eez-open/CF-DIC/EEZ CF-DIC r5B7 Sheet1of3.png

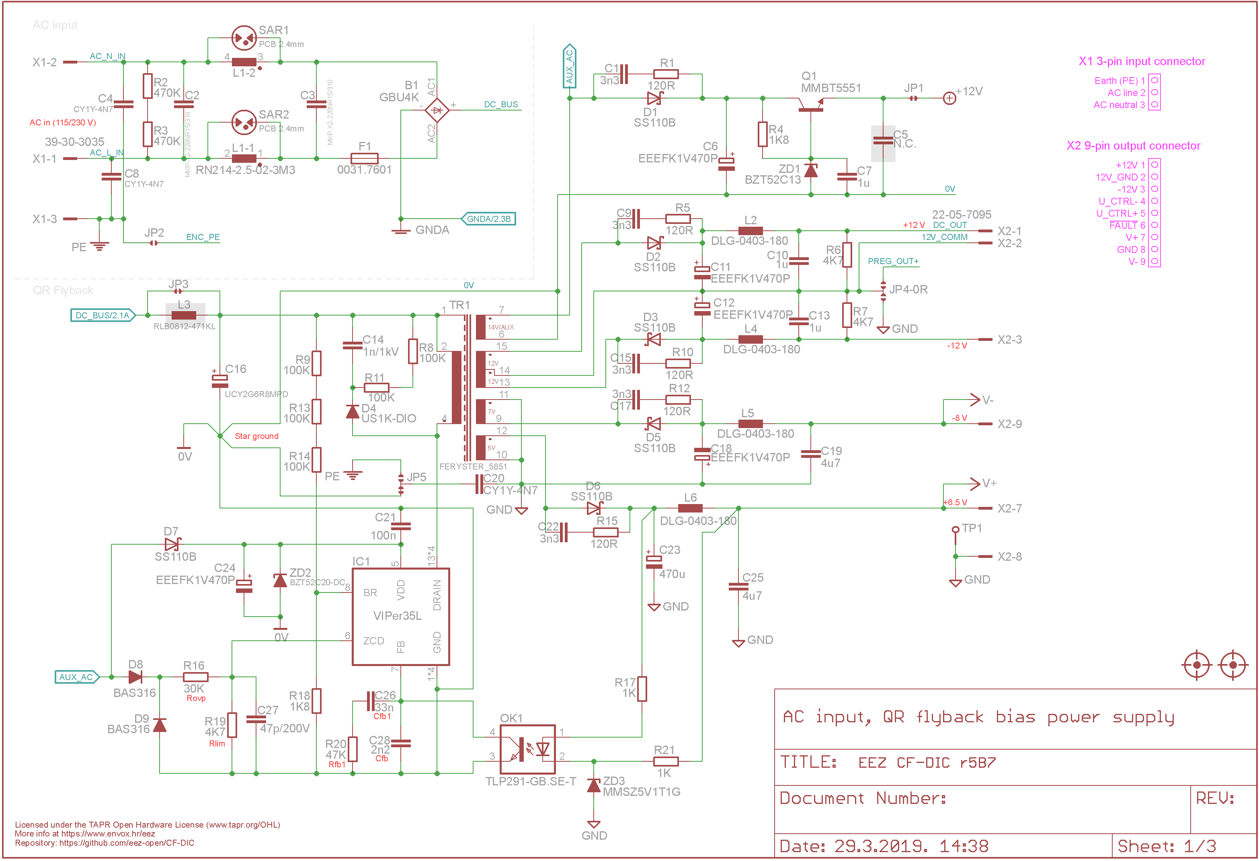
EEZ CF-DIC r5B7 Sheet1of3.png
