eez-open/CF-DIC/EEZ CF-DIC r5B7 Sheet2of3.png

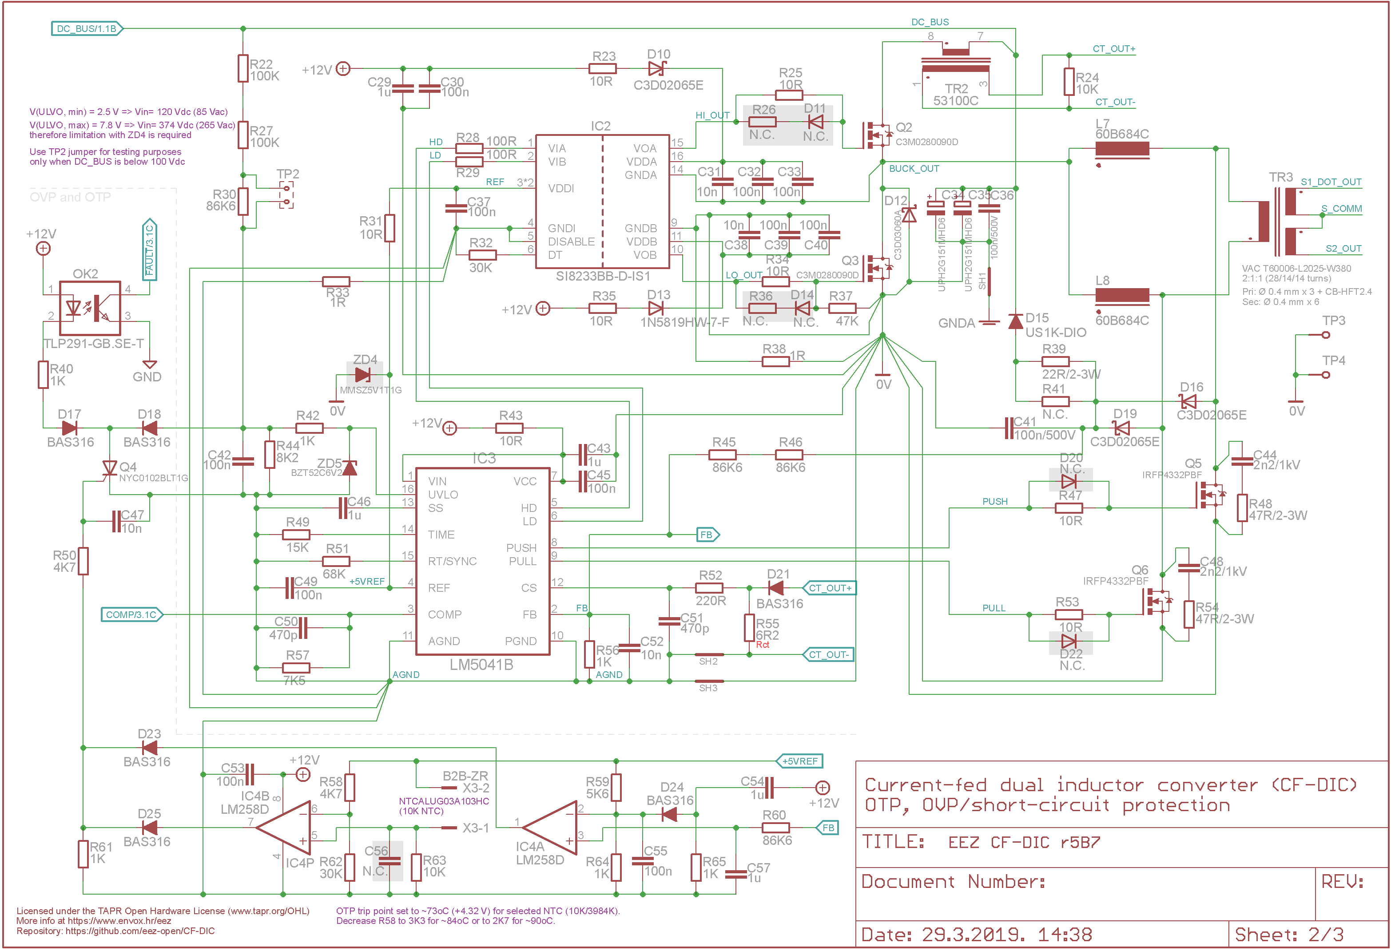
EEZ CF-DIC r5B7 Sheet2of3.png
