eez-open/CF-DIC/Images/CF-DIC_PCB_parts_bottom.png

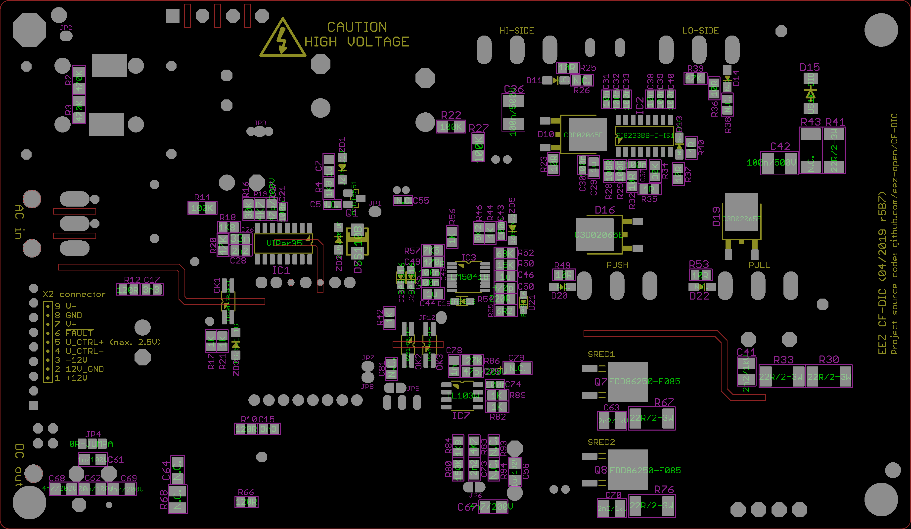
Images/CF-DIC_PCB_parts_bottom.png
