eez-open/CF-DIC/Images/CF-DIC_PCB_parts_top.png

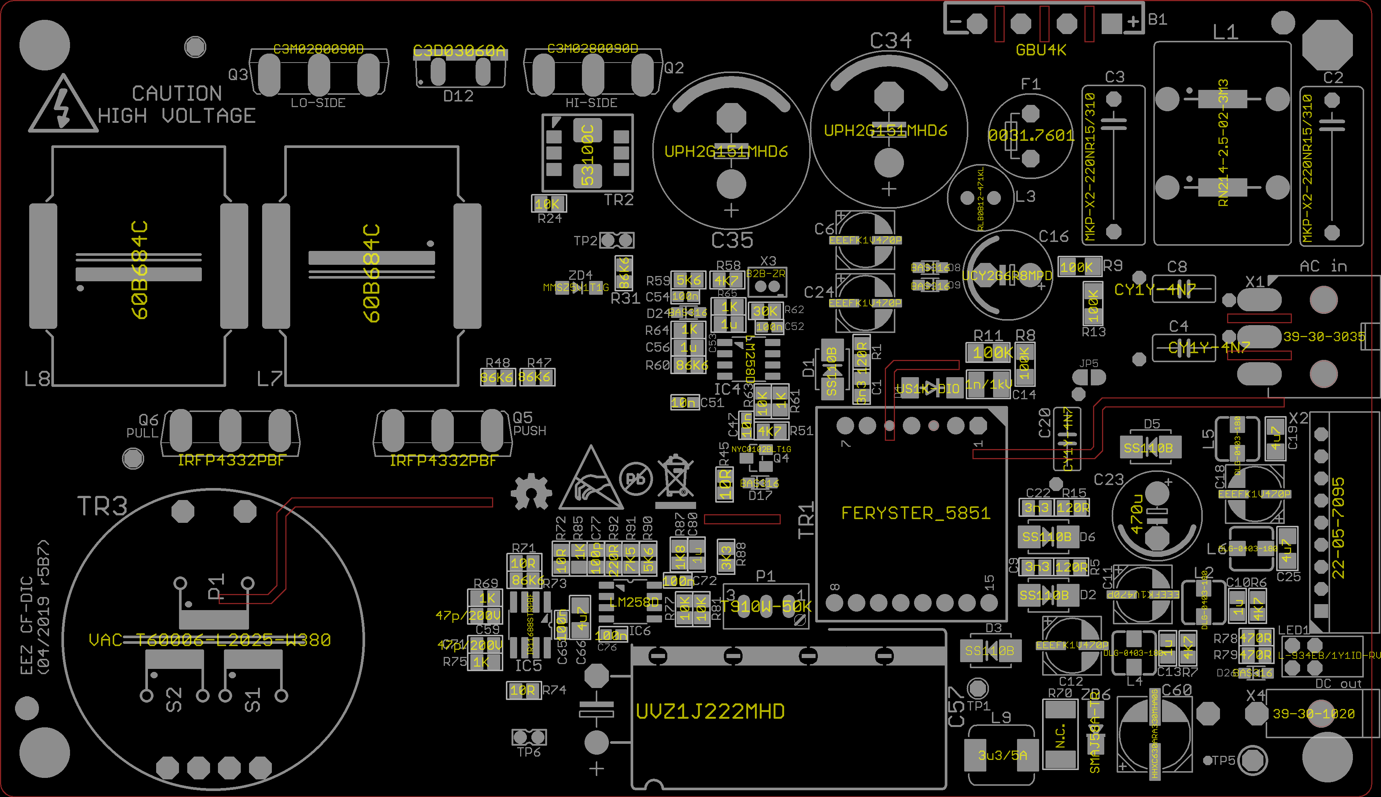
Images/CF-DIC_PCB_parts_top.png
